costonisp/DEC-meetzender/documentation/Si5351+interface/Missing.jpg

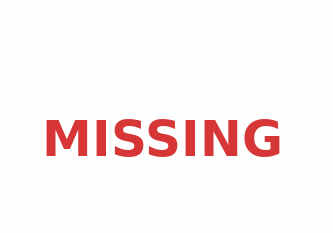
documentation/Si5351+interface/Missing.jpg
