costonisp/DEC-meetzender/documentation/Si5351+interface/BidirectionalDualI2CIsolatorSch.pdf

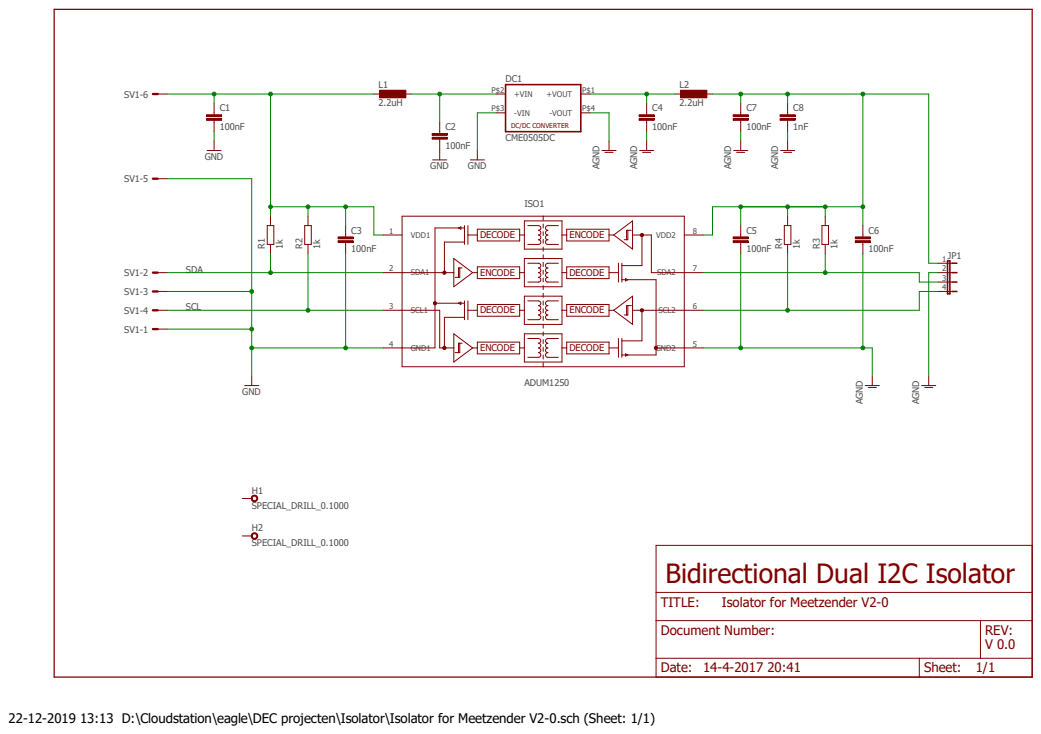
[picture p33: page 1]

Document Number: | REV: V 0.0

Date: 14-4-2017 20:41 | Sheet: 1/1

22-12-2019 13:13 D:\Cloudstation\eagle\DEC projecten\Isolator\Isolator for Meetzender V2-0.sch (Sheet: 1/1)
