costonisp/DEC-meetzender/documentation/Si5351+interface/AdaSi5351Sch.pdf

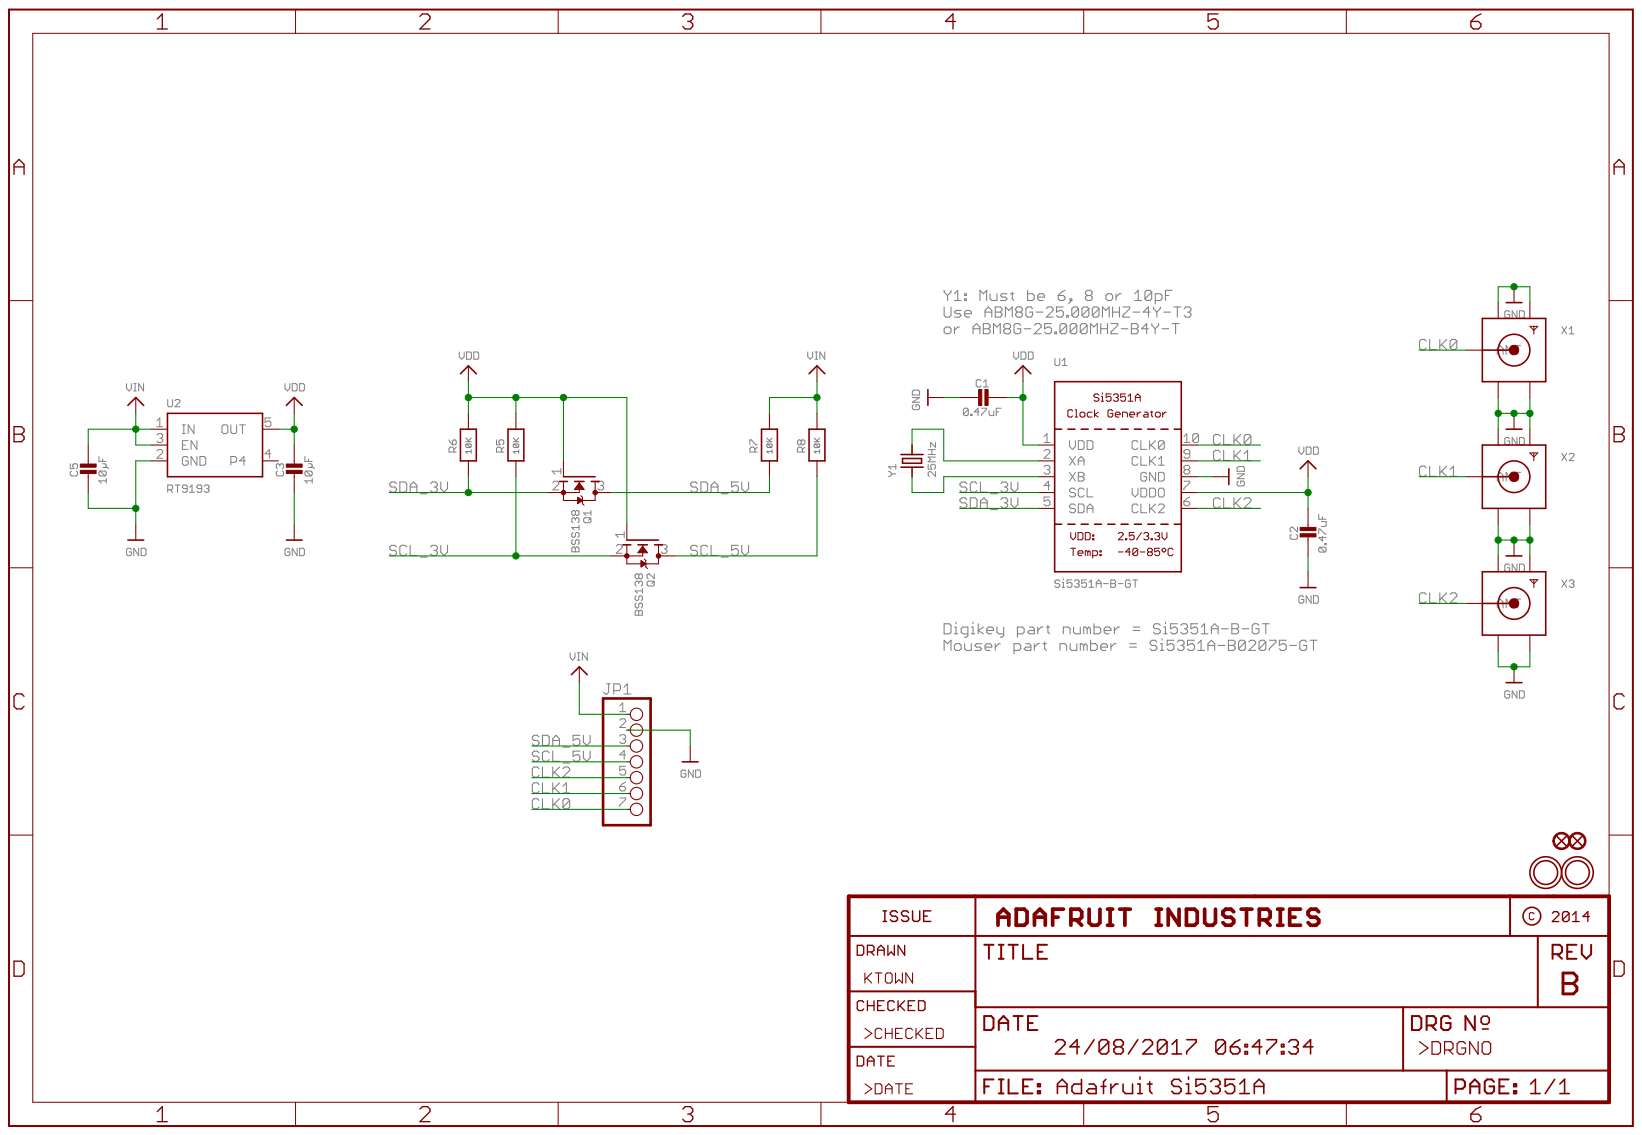
[picture p34: page 1]
